colganr/steel-string-singer-sn-002/3D-CAD-Design/Supplemental JPG exports/4549255643_d4ff51d30e_o.jpg

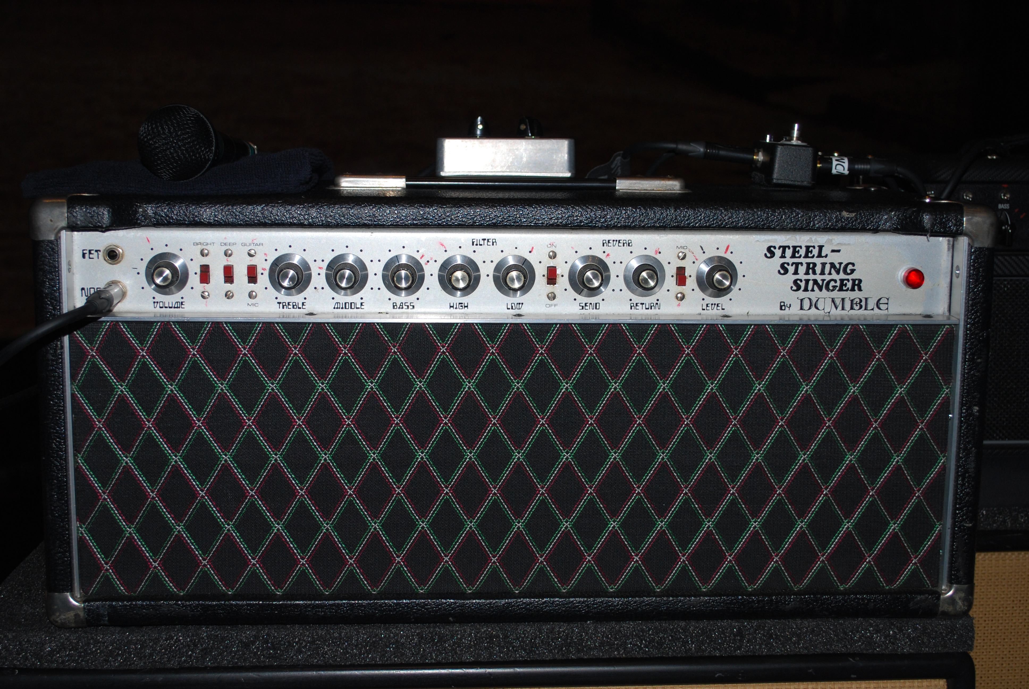
3D-CAD-Design/Supplemental JPG exports/4549255643_d4ff51d30e_o.jpg
