colganr/steel-string-singer-sn-002/3D-CAD-Design/Supplemental JPG exports/font.png

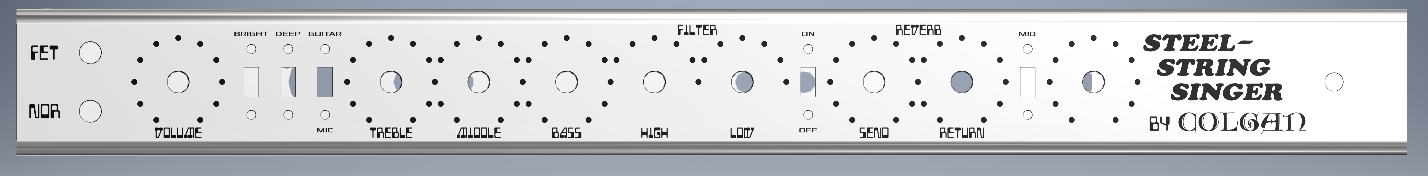
3D-CAD-Design/Supplemental JPG exports/font.png
