colganr/steel-string-singer-sn-002/3D-CAD-Design/Supplemental JPG exports/rear tilt.png

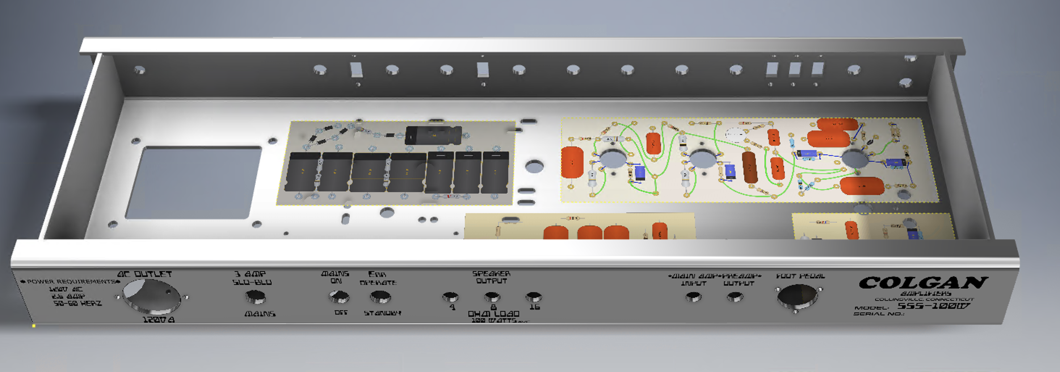
3D-CAD-Design/Supplemental JPG exports/rear tilt.png
