colganr/steel-string-singer-sn-002/Circuit/DIYLC Board JPGs and PDFs/Power Supply Only.png

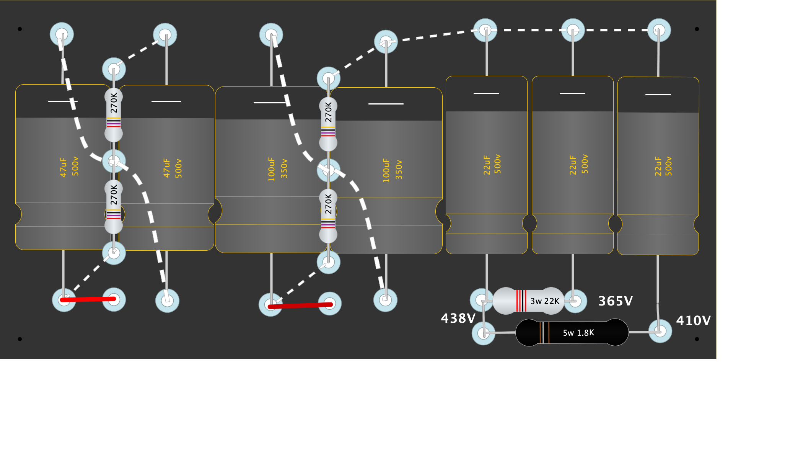
Circuit/DIYLC Board JPGs and PDFs/Power Supply Only.png
