colganr/steel-string-singer-sn-002/Circuit/DIYLC Board JPGs and PDFs/Rectifier Board Only.png

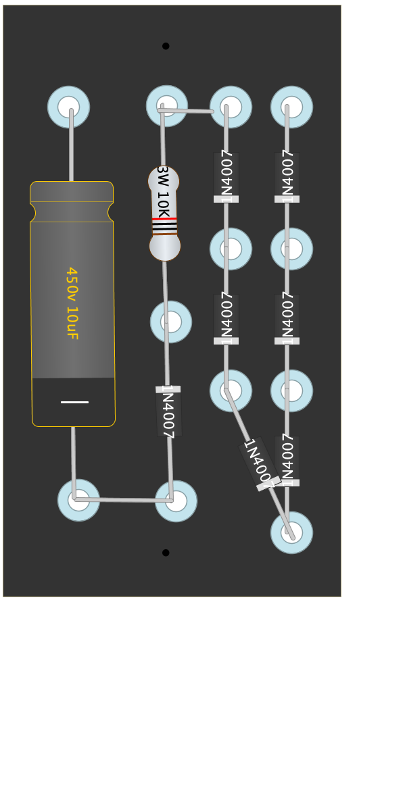
Circuit/DIYLC Board JPGs and PDFs/Rectifier Board Only.png
