colganr/steel-string-singer-sn-002/Reference-Pictures/Full Layout.png

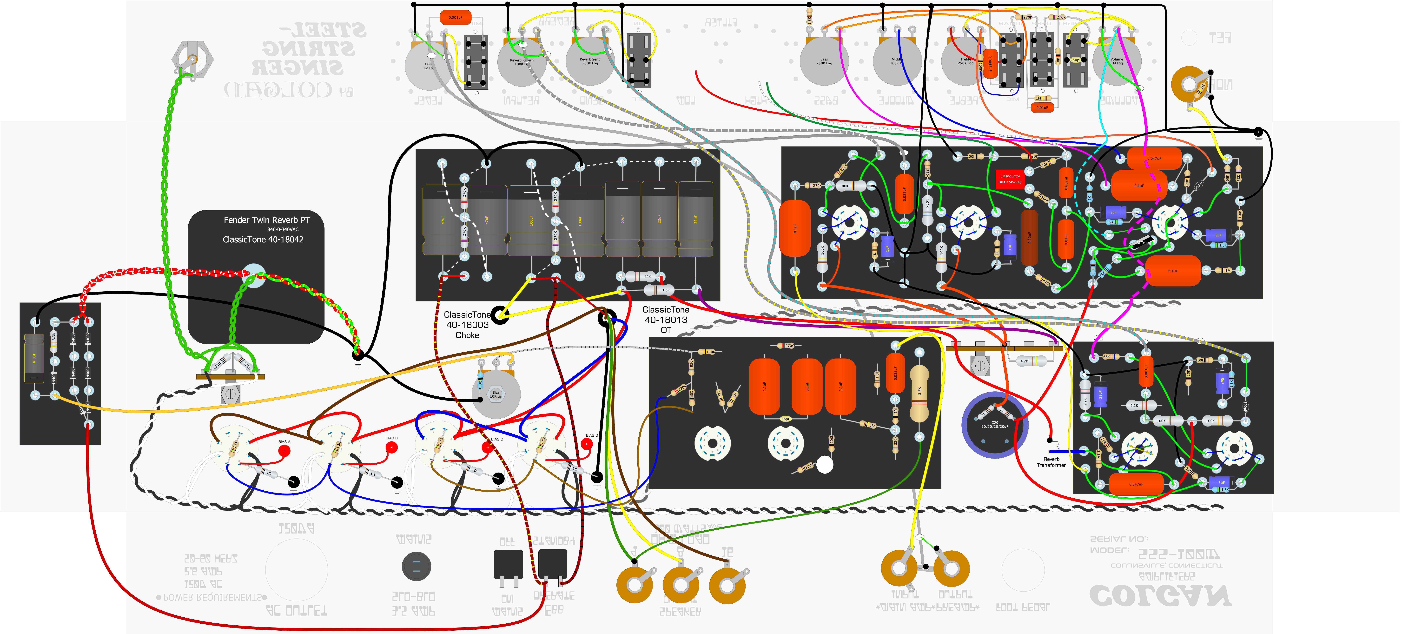
Reference-Pictures/Full Layout.png
