colganr/steel-string-singer-sn-002/Silkscreen-Artwork/SSS 002 Faceplate Reversed.png

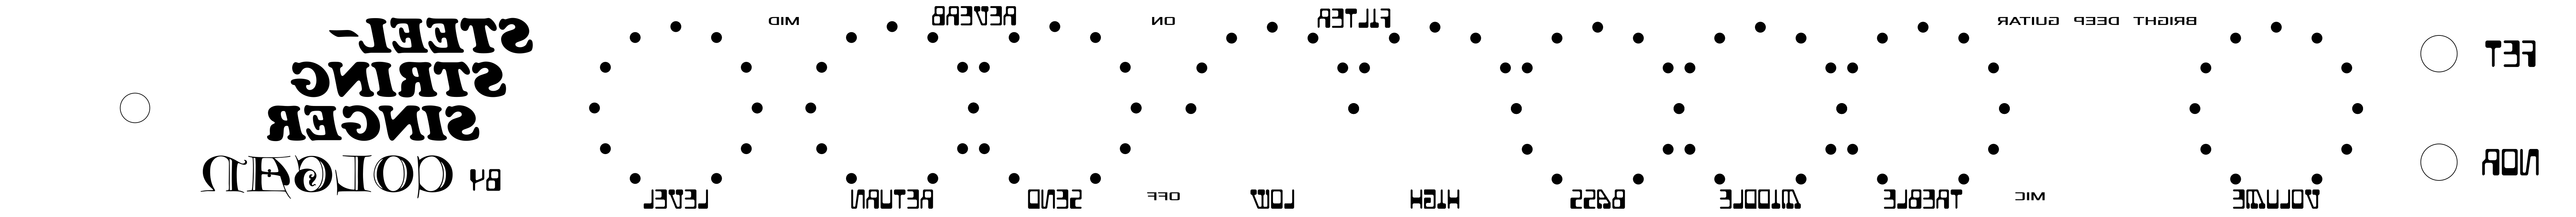
Silkscreen-Artwork/SSS 002 Faceplate Reversed.png
