colganr/steel-string-singer-sn-002/Silkscreen-Artwork/SSS 002 Faceplate.png

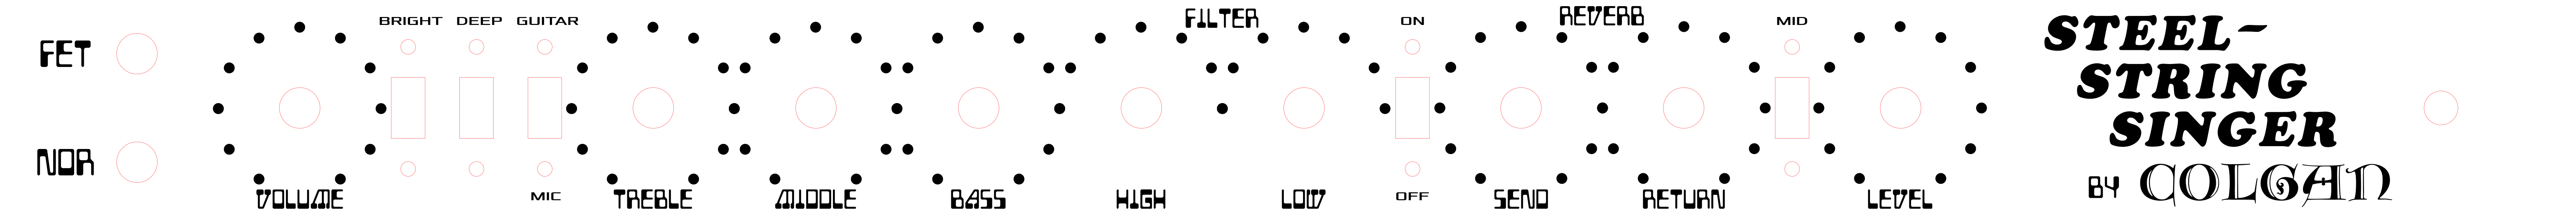
Silkscreen-Artwork/SSS 002 Faceplate.png
