colganr/steel-string-singer-sn-002/Silkscreen-Artwork/SSS 002 Front Wrap.png

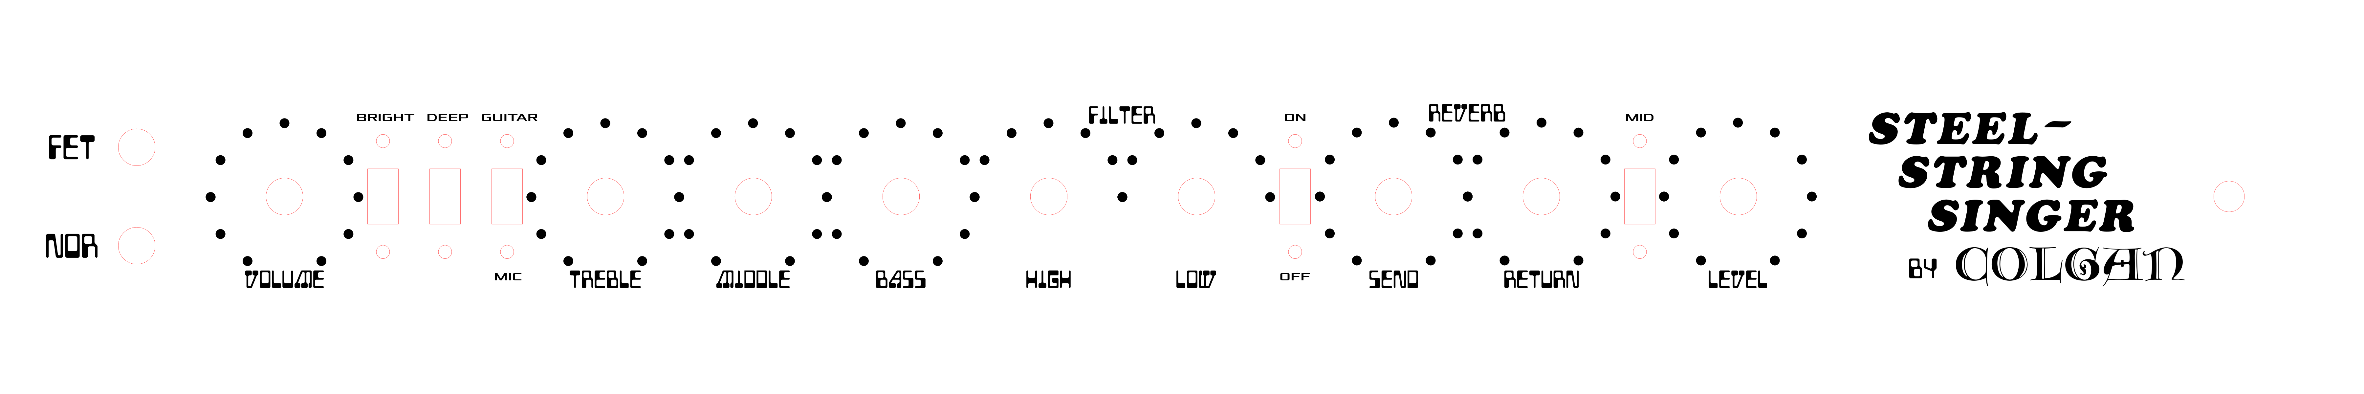
Silkscreen-Artwork/SSS 002 Front Wrap.png
