colganr/steel-string-singer-sn-002/Silkscreen-Artwork/SSS 002 Rear Wrap.png

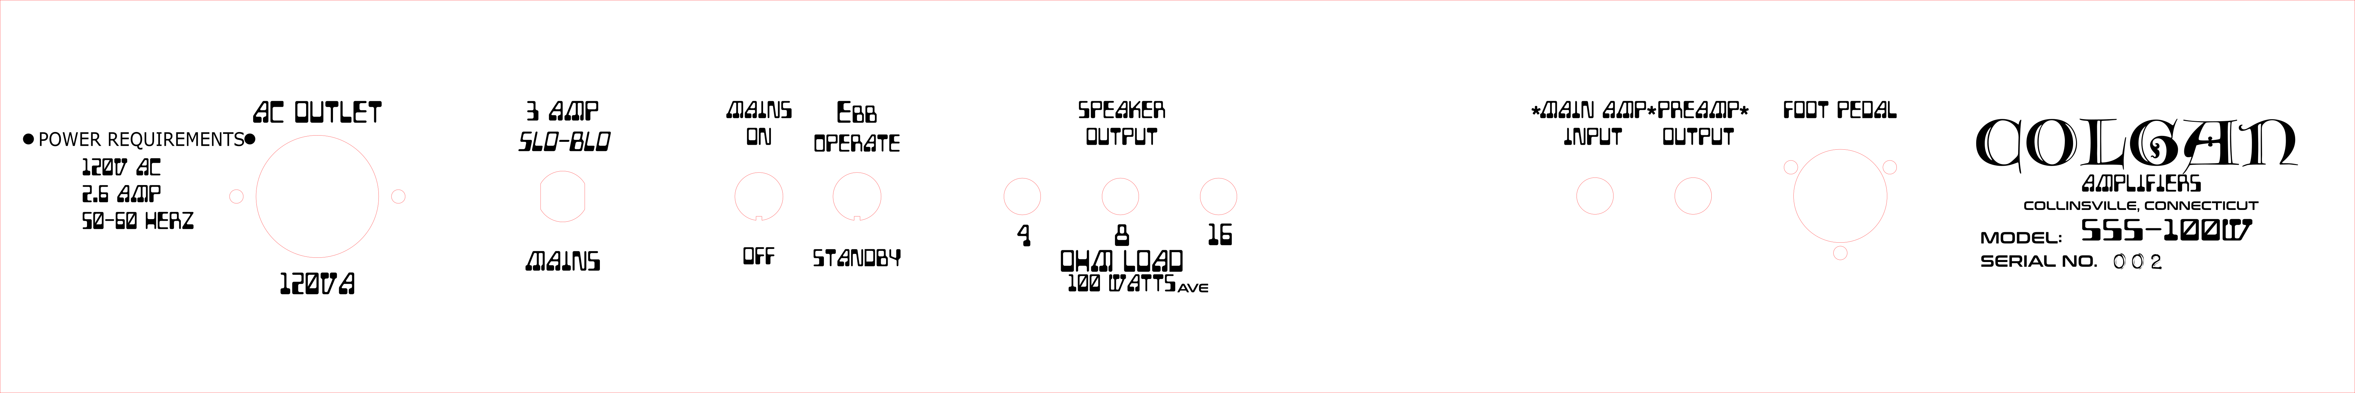
Silkscreen-Artwork/SSS 002 Rear Wrap.png
