colganr/steel-string-singer-sn-002/AutoCAD-Design/PCB outlines/SSS002-[CADSignal].dxf

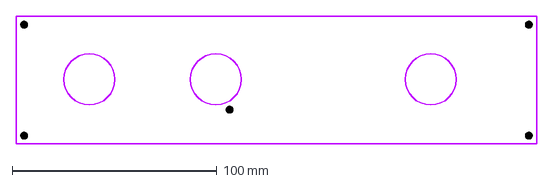
[picture p38: CAD file, 2020-04-30]
AutoCAD-Design/PCB outlines/SSS002-[CADSignal].dxf
254.0 x 62.0 mm
