colganr/steel-string-singer-sn-002/3D-CAD-Design/Supplemental JPG exports/weldInstructions.png

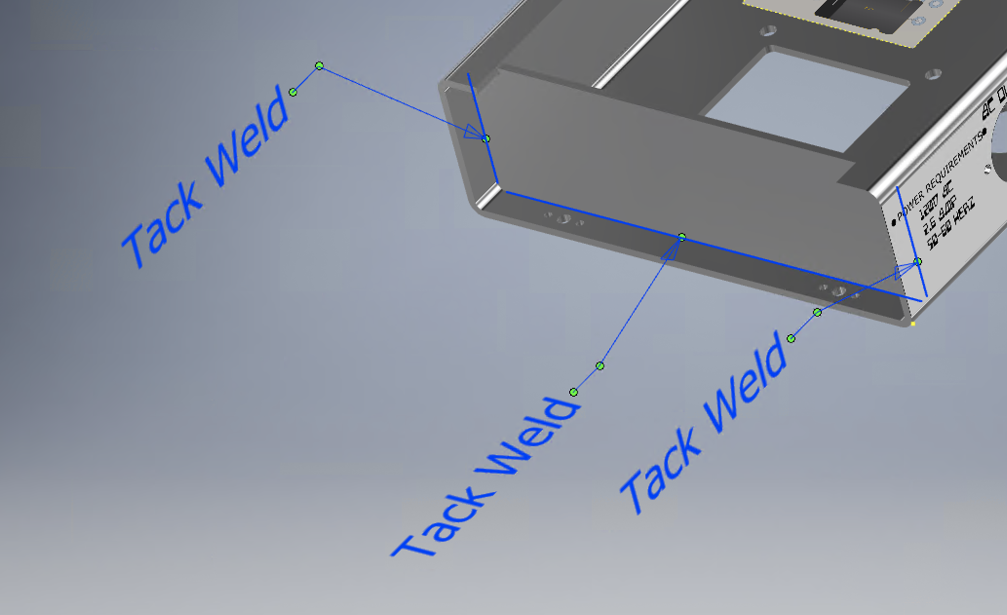
3D-CAD-Design/Supplemental JPG exports/weldInstructions.png
