colganr/steel-string-singer-sn-002/Circuit/DIYLC Board JPGs and PDFs/Preamp Board Only.pdf

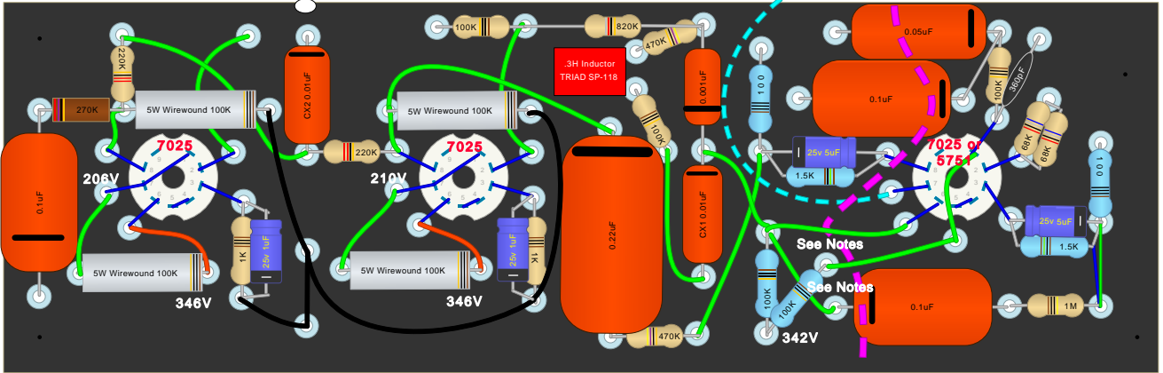
[picture p43: page 1]
5W Wirewound 100K; .3H Inductor TRIAD SP-118; See Notes
