colganr/steel-string-singer-sn-002/Circuit/DIYLC Board JPGs and PDFs/Rectifier Board Only.pdf

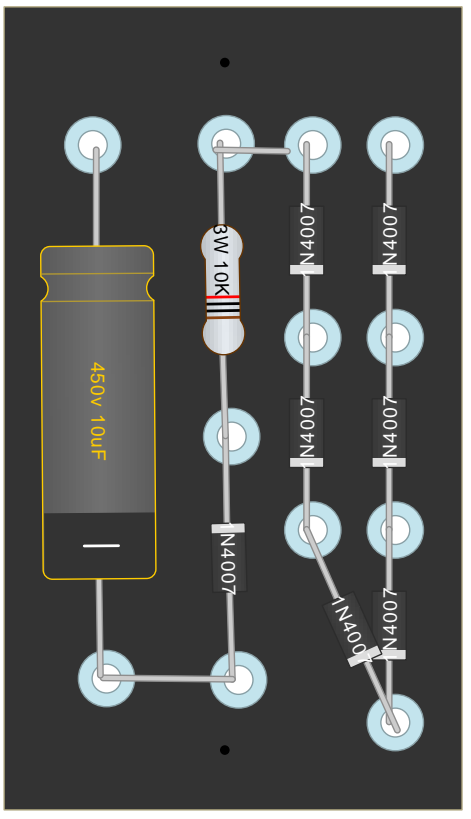
[picture p51: page 1]
