colganr/steel-string-singer-sn-002/Circuit/DIYLC Board JPGs and PDFs/Reverb Board Only.pdf

# 2W 2.2K ⁰.001uF

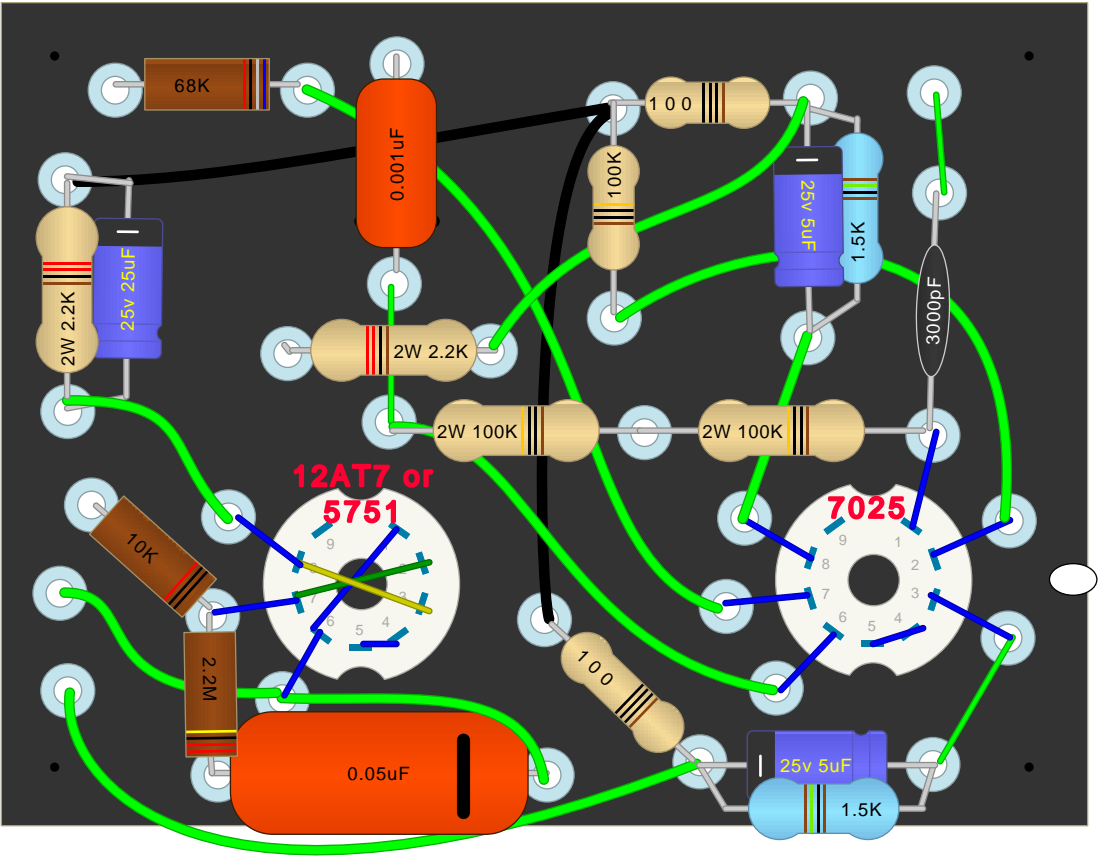
[picture p52: page 1]
